Waps61/Yazz_Winddisplay_ESP32/Nextion/7inch/gauge.png

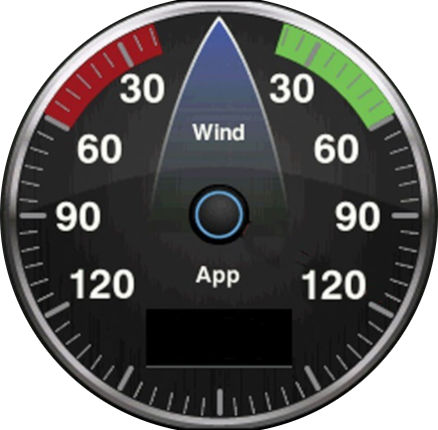
Nextion/7inch/gauge.png
