Waps61/Yazz_Winddisplay_ESP32/Nextion/7inch/HMI faceplate.jpg

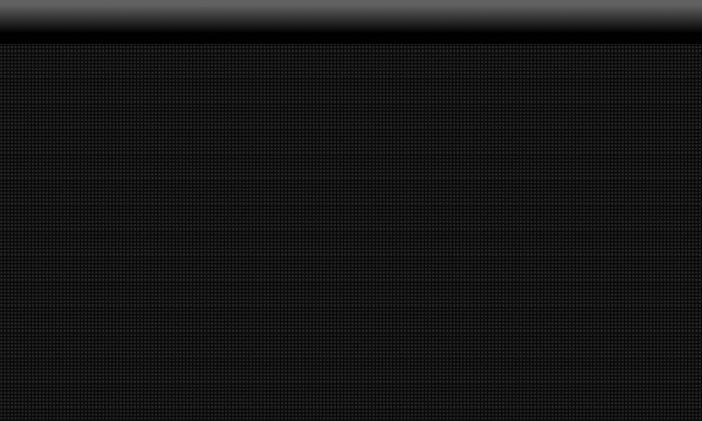
Nextion/7inch/HMI faceplate.jpg
