Waps61/Yazz_Winddisplay_ESP32/Nextion/7inch/HMI faceplate.png

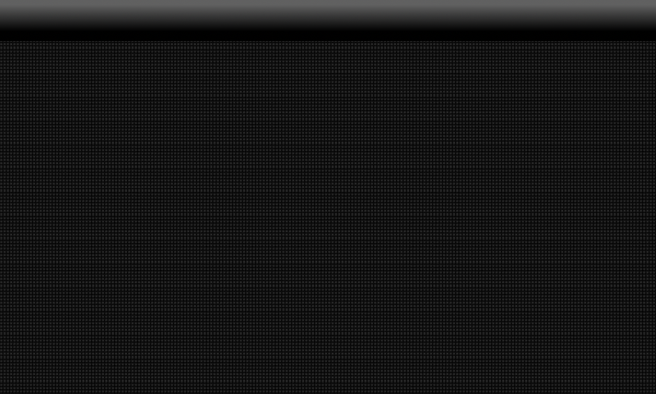
Nextion/7inch/HMI faceplate.png
