Waps61/Yazz_Winddisplay_ESP32/Nextion/7inch/yazz_faceplate_white.png

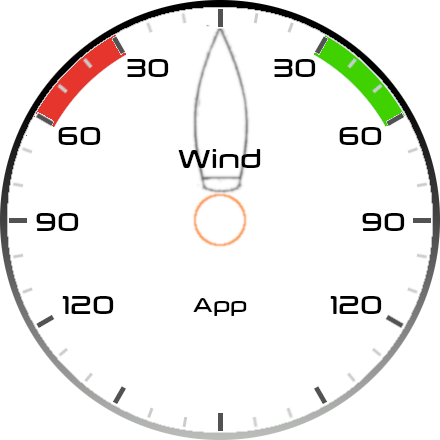
Nextion/7inch/yazz_faceplate_white.png
