Waps61/Yazz_Winddisplay_ESP32/include/NexHardware.h

/**
 * @file NexHardware.h
 *
 * The definition of base API for using Nextion. 
 *
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
 * 02-10-2020 Added function printError for debugging purposes
 */
#ifndef __NEXHARDWARE_H__
#define __NEXHARDWARE_H__
#include <Arduino.h>
#include "NexConfig.h"
#include "NexTouch.h"
#include <HardwareSerial.h>
/**
 * @addtogroup CoreAPI 
 * @{ 
 */

/**
 * Init Nextion.  
 * 
 * @return true if success, false for failure. 
 */
bool nexInit(void);

/**
 * Listen touch event and calling callbacks attached before.
 * 
 * Supports push and pop at present. 
 *
 * @param nex_listen_list - index to Nextion Components list. 
 * @return none. 
 *
 * @warning This function must be called repeatedly to response touch events
 *  from Nextion touch panel. Actually, you should place it in your loop function. 
 */
void nexLoop(NexTouch *nex_listen_list[]);

/**
 * @}
 */

bool recvRetNumber(uint32_t *number, uint32_t timeout = 100);
uint16_t recvRetString(char *buffer, uint16_t len, uint32_t timeout = 100);
void sendCommand(const char* cmd);
bool recvRetCommandFinished(uint32_t timeout = 100);
void printError(uint8_t * errNr);
#endif /* #ifndef __NEXHARDWARE_H__ */
